Refrained-LM/The-Arm-Deck/3d-Files/Buttons/GPIO Bracket.stl

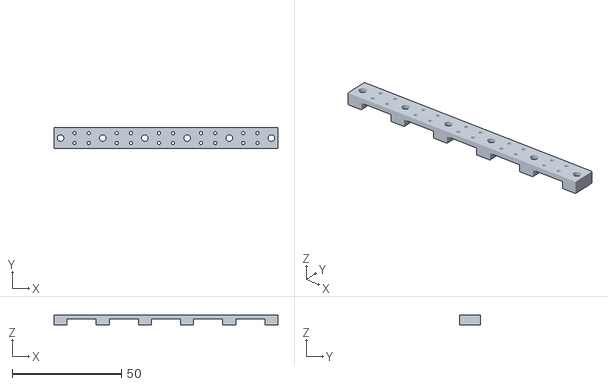
[picture p15: CAD file, 2023-06-06]
3d-Files/Buttons/GPIO Bracket.stl
102.5 x 9.44 x 4.80
